julienrat/ratduino/image1.png

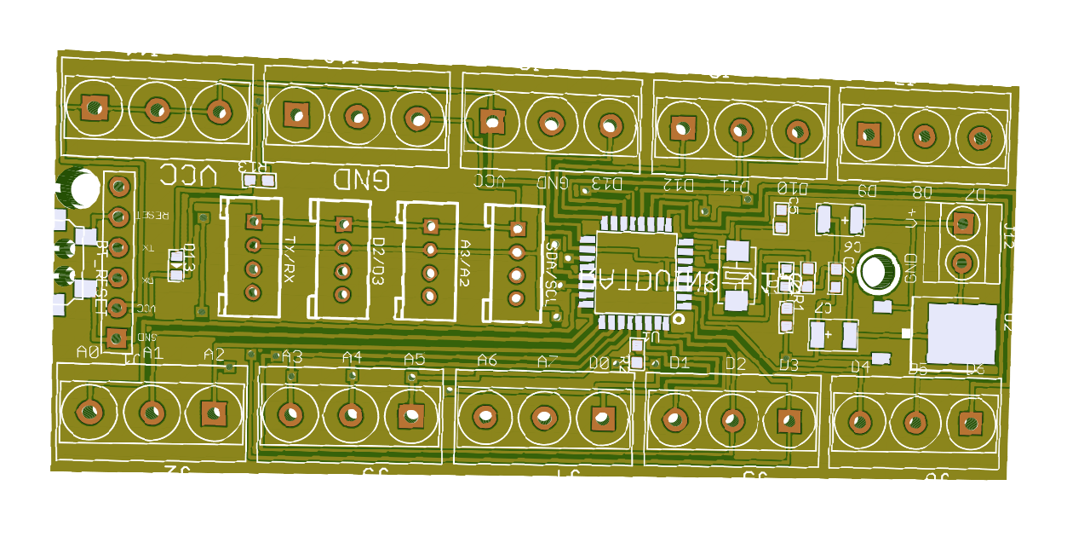
image1.png
